RobertPHeller/DeliveryBox/DeliveryBoxFirmware/DeliveryBoxWebserver.cpp

// -!- C++ -!- //////////////////////////////////////////////////////////////
//
//  System        : 
//  Module        : 
//  Object Name   : $RCSfile$
//  Revision      : $Revision$
//  Date          : $Date$
//  Author        : $Author$
//  Created By    : Robert Heller
//  Created       : 2026-06-17 14:15:08
//  Last Modified : <260711.1553>
//
//  Description	
//
//  Notes
//
//  History
//	
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
static const char rcsid[] = "@(#) : $Id$";

#include <WebServer.h>
#include "Singleton.h"
#include "DeliveryBoxWebserver.h"
#include <libb64/cdecode.h>
#include "Revision.h"
#include "LockServo.h"
#include "LockProcess.h"

static DeliveryBoxWebserver server;
DEFINE_SINGLETON_INSTANCE(DeliveryBoxWebserver);

void DeliveryBoxWebserver::_MainScreen()
{
    _processForm();
    send(200,"text/html", 
         header_("Delivery Box") +
         "<div class='topnav'><h1>Delivery Box</h1></div>" +
         _page() + 
         footer_());
}

String DeliveryBoxWebserver::_page()
{
    String result;
    result += "<div class='content'>";
    if (LockServo::LockServo::IsLocked())
    {
        result += "<h3 style='color:green;'>Box is locked</h3>";
    }
    else
    {
        result += "<h3 style='color:red;'>Box is unlocked</h3>";
    }
    result += "<form method='post' action='/' >\n";
    result += "<div class='card-grid'><div class='card'><ul style='list-style-type: none;'>";
    result += "<li><label for='master-code'>Master Code</label>\n";
    result += "<input type='number' id='master-code' name='master-code' size='8' maxlength='8' /><\li>\n";
    result += "<li><button type='submit' name='set-master' value='true'>Set Master Code</button></li>\n";
    result += "</ul></div></div>";
    result += "</form>\n";
    result += "<form method='post' action='/' >\n";
    result += "<div class='card-grid'><div class='card'><ul style='list-style-type: none;'>";
    result += "<li><label for='one-time'>One Time Code</label>\n";
    result += "<input type='number' id='one-time' name='one-time' size='8' maxlength='8' /></li>\n";
    result += "<li><button type='submit' name='add-one-time' value='true'>Add One Time Code</button></li>\n";
    result += "</ul></div></div>";
    result += "</form>\n";
    result += "</div>";
    return result;
}

void DeliveryBoxWebserver::_processForm()
{
    if (hasArg("set-master"))
    {
        LockProcess::LockProcess::SetMasterCode(arg("master-code"));
    }
    if (hasArg("add-one-time"))
    {
        LockProcess::LockProcess::AddOneTimeCode(arg("one-time"));
    }
}

void DeliveryBoxWebserver::_notFound()
{
    send(404, "text/html", 
         header_("File Not Found") + 
         "<div class='topnav'><h1>File Not Found</h1></div>" +
         footer_());
}

void DeliveryBoxWebserver::_sendStyle()
{
    send(200, "text/css", R"stylesheet(
html {
    font-family: Arial, Helvetica, sans-serif;
    display: inline-block;
    text-align: center;
}
h1 {
    font-size: 1.8rem;
    color: white;
}
body {
    margin: 0;
    background-color: #cccccc;
    font-family: Arial, Helvetica, Sans-Serif;
    Color: #000088;
}
.topnav {
    overflow: hidden;
    background-color: #0A1128;
}
.content {
    padding: 50px;
}
.card-grid {
    max-width: 800px;
    margin: 0 auto;
    margin-bottom: 30px;
    display: grid;
    grid-gap: 2rem;
    grid-template-columns: repeat(auto-fit, minmax(300px, 1fr));
}
.card {
    background-color: white;
    box-shadow: 2px 2px 12px 1px rgba(140,140,140,.5);
}
button {
    color: white;
    padding: 14px 20px;
    margin: 8px 0;
    border: none;
    cursor: pointer;
    border-radius: 4px;
}

.gray-label {
    color: #bebebe;
    font-size: 1rem;
}

}
)stylesheet");
}

void DeliveryBoxWebserver::_sendJavaScript()
{
    send(200, "text/javascript" , R"javascript(
function dummy()
{
}
)javascript");
}

String DeliveryBoxWebserver::header_(String title)
{    return String(R"html(
<html>
<head>
<title>)html" + title + R"html(</title>
<meta http-equiv="content-language" content="en" />
<meta name="generator" content=")html" PROGRAM_NAME ":" REVISION_GIT_HASH R"html(" />
<link rel="stylesheet" href="/style.css" type="text/css" />
<script type="text/javascript" src="/javascript.js" />
</head>
<body>)html");
}

String DeliveryBoxWebserver::footer_()
{
    return String(R"html(
<footer id="colophon" class="site-footer" role="contentinfo">
<p><img src="/Robot1-110.png" width="63" height="110" alt="Country Robot" style="float:left;" />&copy; 2024 Robert Heller D/B/A Deepwoods Software (The Country Robot)</p>
<p><a href="https://www.thecountryrobot.com/">Created by Robert Heller</a></p>
<p><a href="https://github.com/RobertPHeller/DeliveryBox">Full project here.</a></p>
</footer>
</body>
</html>)html");
}
          
#include "Robot1-110.h"
void DeliveryBoxWebserver::_sendRobot1_110()
{
    uint8_t buffer[base64_decode_expected_len(sizeof(ROBOT1_110))];
    int status = base64_decode_chars(ROBOT1_110,sizeof(ROBOT1_110),(char *)buffer);
    send(200,"image/png",String((const char *)buffer));
}
