RobertPHeller/DeliveryBox/DeliveryBoxFirmware/LockProcess.cpp

// -!- C++ -!- //////////////////////////////////////////////////////////////
//
//  System        : 
//  Module        : 
//  Object Name   : $RCSfile$
//  Revision      : $Revision$
//  Date          : $Date$
//  Author        : $Author$
//  Created By    : Robert Heller
//  Created       : 2026-06-18 21:08:59
//  Last Modified : <260629.1106>
//
//  Description	
//
//  Notes
//
//  History
//	
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
static const char rcsid[] = "@(#) : $Id$";


#include <Arduino.h>
#include "Display.h"
#include "LockServo.h"
#include "Singleton.h"
#include <FS.h>
#include <SPIFFS.h>
#include <vector>
#include "LockProcess.h"
#include <string.h>

namespace LockProcess {

static LockProcess lockProcessor;
DEFINE_SINGLETON_INSTANCE(LockProcess);


static const char *LOCKED = "LOCKED";
static const char *UNLOCKED = "UNLOCKED";

LockProcess::LockProcess()
{
}

void LockProcess::_begin()
{
    _loadMasterCode();
    _loadOneTimeCodes();
    LockServo::LockServo::unlock();
    memset(_buffer,0,sizeof(_buffer));
    _bufferIndex = 0;
    Display::Display::ClearDisplay();
    _message(UNLOCKED);
}

void LockProcess::_loadMasterCode()
{
    File fp = SPIFFS.open("/master.txt");
    if (fp)
    {
        _MasterCode = fp.readStringUntil('\r');
        fp.close();
    }
    else
    {
        _MasterCode = "99999999"; // default master code.
    }
}

void LockProcess::_loadOneTimeCodes()
{
    _OneTimeCodes.clear();
    File fp = SPIFFS.open("/onetimecodes.txt");
    if (fp)
    {
        do
        {
            String code = fp.readStringUntil('\r');
            _OneTimeCodes.push_back(code);
            if (fp.peek() == '\n') fp.read();
        } while(fp);
        fp.close();
    }
}

void LockProcess::_rewriteOneTimeCodes()
{
    File fp = SPIFFS.open("/onetimecodes.txt", FILE_WRITE);
    if (fp)
    {
        for (auto ic = _OneTimeCodes.begin(); ic != _OneTimeCodes.end(); ic++)
        {
            fp.println(*ic);
        }
        fp.close();
    }
}

void LockProcess::_setmaster(String newcode)
{
    File fp = SPIFFS.open("/master.txt", FILE_WRITE);
    if (fp)
    {
        fp.println(newcode);
        fp.close();
        _loadMasterCode();
    }
}

void LockProcess::_addonetime(String newcode)
{
    File fp = SPIFFS.open("/onetimecodes.txt", FILE_APPEND);
    if (fp)
    {
        fp.println(newcode);
        fp.close();
        _loadOneTimeCodes();
    }
}

void LockProcess::_message(const char *m)
{
    Display::Display::ClearDisplay();
    for (const char *p = m; *p; p++)
    {
        Display::Display::WriteCharacter((uint8_t) *p);
    }
}

void LockProcess::_processKey(uint8_t k)
{
    if (_bufferIndex == 0) Display::Display::ClearDisplay();
    if (_bufferIndex < CODELEN)
    {
        Display::Display::WriteCharacter(k);
        _buffer[_bufferIndex++] = (char) k;
    }
    if (LockServo::LockServo::IsLocked())
    {
        if (_MasterCode == _buffer)
        {
            LockServo::LockServo::unlock();
            memset(_buffer,0,sizeof(_buffer));
            _bufferIndex = 0;
            Display::Display::ClearDisplay(); 
            _message(UNLOCKED);
            return;
        }
        for (auto ic = _OneTimeCodes.begin(); ic != _OneTimeCodes.end(); ic++)
        {
            if (*ic == _buffer)
            {
                _OneTimeCodes.erase(ic);
                _rewriteOneTimeCodes();
                LockServo::LockServo::unlock();
                memset(_buffer,0,sizeof(_buffer));
                _bufferIndex = 0;
                Display::Display::ClearDisplay(); 
                _message(UNLOCKED);
                return;
            }
        }
    }
    else
    {
        if (String("***") == _buffer)
        {
            LockServo::LockServo::lock();
            memset(_buffer,0,sizeof(_buffer));
            _bufferIndex = 0;
            Display::Display::ClearDisplay();
            _message(LOCKED);
            return;
        }
    }
}

void LockProcess::_displayCurrentLockState()
{
    if (LockServo::LockServo::IsLocked())
    {
        _message(LOCKED);
    }
    else
    {
        _message(UNLOCKED);
    }
}
        
}
