RobertPHeller/DeliveryBox/DeliveryBoxFirmware/LockProcess.h

// -!- C++ -!- //////////////////////////////////////////////////////////////
//
//  System        : 
//  Module        : 
//  Object Name   : $RCSfile$
//  Revision      : $Revision$
//  Date          : $Date$
//  Author        : $Author$
//  Created By    : Robert Heller
//  Created       : 2026-06-18 20:56:22
//  Last Modified : <260628.2045>
//
//  Description	
//
//  Notes
//
//  History
//	
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
#ifndef __LOCKPROCESS_H
#define __LOCKPROCESS_H

#include <Arduino.h>
#include "Display.h"
#include "LockServo.h"
#include "Singleton.h"
#include <FS.h>
#include <SPIFFS.h>
#include <vector>

namespace LockProcess {

/** Class to manage locking and unlocking and storing the unlock codes.
 * Manages one master code and any number of one-time codes.
 */
class LockProcess : public Singleton<LockProcess>
{
public:
    /** Constructor. */
    LockProcess();
    /** Initializer.  Loads the codes from SPIFFS (SPI Flash File System).
     */
    static void Initialize()
    {
        instance()->_begin();
    }
    /** Process a key. If enough digits have been entered and if they match
     * a code, unlock the box.
     * If the box is unlocked and three stars (*) have been entered, lock the
     * box.
     * @param k The entered key (0-9, # and *).
     */
    static void ProcessKey(uint8_t k)
    {
        instance()->_processKey(k);
    }
    /** Set the master code.
     * Saves a new master code to the SPIFFS (SPI Flash File System).
     * @param newcode The new code.
     */
    static void SetMasterCode(String newcode)
    {
        instance()->_setmaster(newcode);
    }
    /** Add a one time code.
     * Appends a one time code to the end of the list of one time codes.
     * @param newcode The new code. 
     */
    static void AddOneTimeCode(String newcode)
    {
        instance()->_addonetime(newcode);
    }
    static void DisplayCurrentLockState()
    {
        instance()->_displayCurrentLockState();
    }
private:
    void _begin();
    void _loadMasterCode();
    void _loadOneTimeCodes();
    void _processKey(uint8_t k);
    void _message(const char *m);
    void _setmaster(String newcode);
    void _addonetime(String newcode);
    void _rewriteOneTimeCodes();
    void _displayCurrentLockState();
    static constexpr size_t CODELEN = 9;
    char _buffer[CODELEN];
    size_t _bufferIndex;
    String _MasterCode;
    std::vector<String> _OneTimeCodes;
};


}

#endif // __LOCKPROCESS_H
