RobertPHeller/DeliveryBox/DeliveryBoxFirmware/Revision.py

#*****************************************************************************
#
#  System        : 
#  Module        : 
#  Object Name   : $RCSfile$
#  Revision      : $Revision$
#  Date          : $Date$
#  Author        : $Author$
#  Created By    : Robert Heller
#  Created       : Thu Aug 15 16:55:29 2024
#  Last Modified : <260617.0711>
#
#  Description	
#
#  Notes
#
#  History
#	
#*****************************************************************************
#
#    Copyright (C) 2024  Robert Heller D/B/A Deepwoods Software
#			51 Locke Hill Road
#			Wendell, MA 01379-9728
#
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
# 
#
#*****************************************************************************


from optparse import OptionParser
import subprocess
import os
import time
import platform
import getpass
import filecmp

f_null = open(os.devnull, "w")
usage = "usage: %prog [options]\n\n" + \
    "  %prog -i $(APP_PATH) -o revisions.h\n"
    
parser = OptionParser(usage=usage)
parser.add_option("-o", "--output", dest="output", metavar="FILE",
                  default="Revision",
                  help="generated output files (without the file extentions)")
parser.add_option("-d", "--dirty", dest="dirty", action="store_true",
                  default=False,
                  help="add the \"dirty\" suffix: -d")
parser.add_option("-t", "--time", dest="date", action="store_true",
                  default=False,
                  help="add the date/time to the output")
parser.add_option("-H", "--host", dest="hostname", action="store_true",
                  default=False,
                  help="add the hostname to the output")
parser.add_option("-U", "--username", dest="username", action="store_true",
                  default=False,
                  help="add the username and hostname to the output")
                                                                        
(options, args) = parser.parse_args()

inputs = '..'

orig_dir = os.path.abspath('./')

#initialize hxx output to nothing
outputhxx = ''
outputdoc = '/** @page Revision Build Revisions'

# add data/time
if options.date :
    now = time.strftime("%a, %d %b %Y %H:%M:%S %Z")
    outputhxx += '\n#define BUILD_TIME "' + now + '"\n'
    outputdoc += "\n * - Build time: " + now

# add user and host names
if options.username or options.hostname :
    outputhxx += '\n#define BUILT_BY "'
    outputdoc += "\n * - Built by: "
    if options.username :
        username = getpass.getuser() + '@'
        outputhxx += username
        outputdoc += getpass.getuser() + '\\@'
    if options.hostname :
        hostname = platform.node()
        outputhxx += hostname
        outputdoc += hostname
    outputhxx +='"\n'
    

main_git_hash = None

# go into the root of the repo
os.chdir(orig_dir)

# get the short hash
git_hash = subprocess.check_output(['git', 'rev-parse', '--short', 'HEAD'])
git_hash = str(git_hash[:7].decode())

# get the dirty flag
dirty = os.system('git diff --quiet')

hashopts = ""

if dirty :
    hashopts += ':-d'
if main_git_hash is None:
    main_git_hash = git_hash + hashopts

outputhxx = outputhxx[:-1]
if main_git_hash is not None:
    outputhxx += '\n#define PROGRAM_NAME "' + os.path.split(os.path.abspath(orig_dir))[1] + '"\n'
    outputhxx += '\n#define REVISION_GIT_HASH "' + main_git_hash + '"\n'
    outputdoc += "\n * - Program Name: " + os.path.split(os.path.abspath(orig_dir))[1]
    outputdoc += "\n * - Git Hash: " + main_git_hash

os.chdir(orig_dir)

# generate the *.hxxout file
output_file = open(options.output + 'Try.h', 'w')
output_file.write(outputdoc + "\n */\n\n")
output_file.write(outputhxx)
output_file.close()
# because a build may always run the script, we only want to replace the actual
# output files that get built if something has changed

diffhxx = subprocess.call(["diff",
                           "-I", """Sun, """, "-I", """Mon, """,
                           "-I", """Tue, """, "-I", """Wed, """,
                           "-I", """Thu, """, "-I", """Fri, """,
                           "-I", """Sat, """,
                           options.output + 'Try.h',
                           options.output + '.h'],
                          stdout=f_null, stderr=f_null)

# disable this because we are not actually writing a cxx file above.
diffcxx = 0

if diffhxx != 0 :
    os.system('rm -f ' + options.output + '.h')
    os.system('mv ' + options.output + 'Try.h ' + options.output + '.h')



os.system('rm -f ' + options.output + 'Try.h')
f_null.close()
